wurthless-elektroniks/scart-breakout/gerbs/v2-do-not-use/snore.png

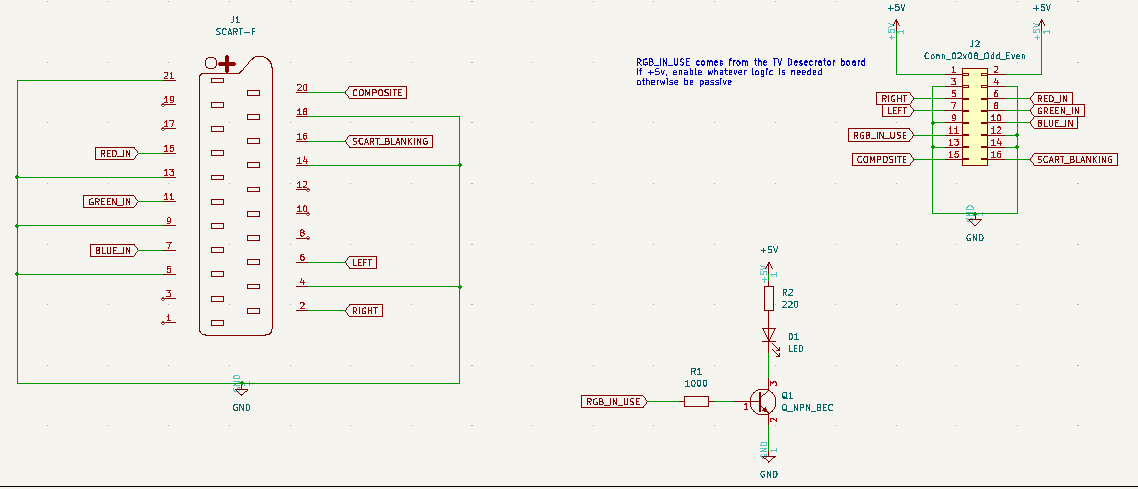
gerbs/v2-do-not-use/snore.png
